gfvalvo/TeensyPOV/Hardware/20180509_212900.jpg

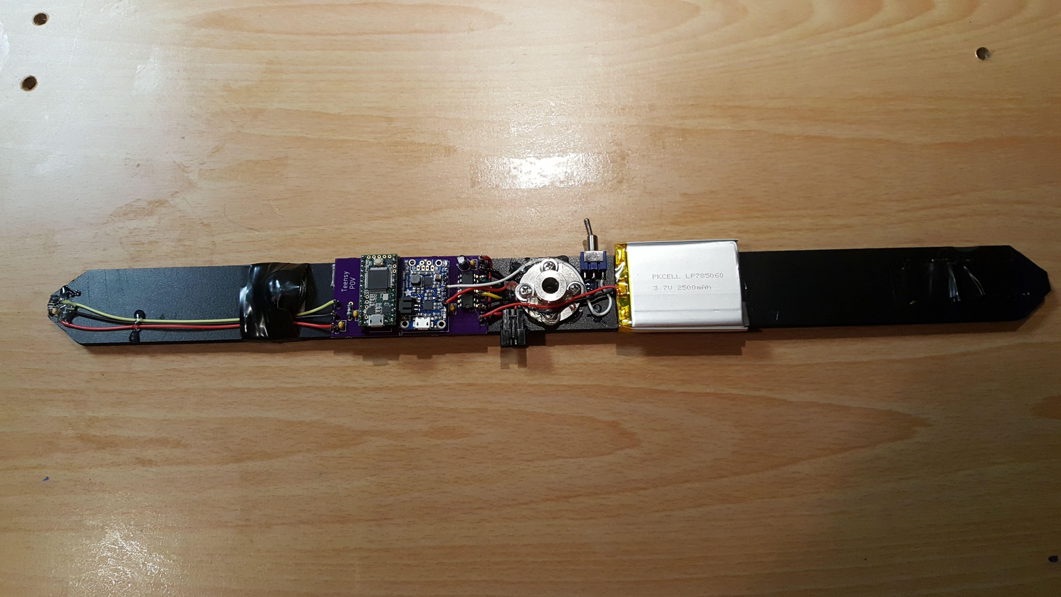
Hardware/20180509_212900.jpg
