gfvalvo/TeensyPOV/textCharacters.cpp

// MSB = topmost pixel on column
// Lowest index = leftmost column of character
// Each element in the data array is the state of one column in the letter.

#include "textCharacters.h"

const pov_char textCharacters::font_numbers[] = { { 0b0111110, 0b1000101,
		0b1001001, 0b1010001, 0b0111110, }, // 0
		{ 0b0000000, 0b0100001, 0b1111111, 0b0000001, 0b0000000, }, // 1
		{ 0b0100001, 0b1000011, 0b1000101, 0b1001001, 0b0110001, }, // 2
		{ 0b1000010, 0b1000001, 0b1010001, 0b1101001, 0b1000110, }, // 3
		{ 0b0001100, 0b0010100, 0b0100100, 0b1111111, 0b0000100, }, // 4
		{ 0b1110010, 0b1010001, 0b1010001, 0b1010001, 0b1001110, }, // 5
		{ 0b0011110, 0b0101001, 0b1001001, 0b1001001, 0b0000110, }, // 6
		{ 0b1100000, 0b1000000, 0b1000111, 0b1001000, 0b1110000, }, // 7
		{ 0b0110110, 0b1001001, 0b1001001, 0b1001001, 0b0110110, }, // 8
		{ 0b0110000, 0b1001001, 0b1001001, 0b1001010, 0b0111100, }, // 9
		};

const pov_char textCharacters::font_uppercase[] = { { 0b0111111, 0b1000100,
		0b1000100, 0b1000100, 0b0111111, }, // A
		{ 0b1111111, 0b1001001, 0b1001001, 0b1001001, 0b0110110, }, // B
		{ 0b0111110, 0b1000001, 0b1000001, 0b1000001, 0b0100010, }, // C
		{ 0b1111111, 0b1000001, 0b1000001, 0b0100010, 0b0011100, }, // D
		{ 0b1111111, 0b1001001, 0b1001001, 0b1001001, 0b1000001, }, // E
		{ 0b1111111, 0b1001000, 0b1001000, 0b1001000, 0b1000000, }, // F
		{ 0b0111110, 0b1000001, 0b1001001, 0b1001001, 0b0101111, }, // G
		{ 0b1111111, 0b0001000, 0b0001000, 0b0001000, 0b1111111, }, // H
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
				flippedColumn <<= 1;
				flippedColumn |= orignalColumn & 0b1;
				orignalColumn >>= 1;
			}
			*(matrixBuffer++) = flippedColumn;
		}
	} else {
		for (index1 = 0; index1 < 5; index1++) {
			*(matrixBuffer++) = currentCharMatrix->data[index1];
		}
	}
}
