gfvalvo/TeensyPOV/examples/MultipleDisplays/picture.cpp

/*
 * picture.cpp
 *
 *  Created on: Mar 30, 2018
 *      Author: GFV
 */
#include <stdint.h>
#include "TeensyPOV.h"
extern const LedArrayStruct pictureStruct;

static const uint8_t logNumSegments = TeensyPOV::LOG_256_SEGMENTS;
static const uint32_t numColorBits = TeensyPOV::COLOR_BITS_4;
static const uint32_t tdcDisplaySegment = 0;

static const uint32_t pictureArray[][5] = { { 0x11111111, 0x22BC2111,
		0x11111190,
		0x11111111, 0x00000011 }, { 0x11111111, 0x22BC2111, 0x11111190,
		0x11111111, 0x00000011 }, { 0x11111111, 0x22222111, 0x11111102,
		0x11111111, 0x00000011 }, { 0x11111111, 0xB2222111, 0x11111110,
		0x11111111, 0x00000611 }, { 0x11111111, 0xB222D111, 0x11111110,
		0x11111111, 0x00000511 }, { 0x11111111, 0x0002D111, 0x11111020,
		0x11111111, 0x00000511 }, { 0x11111111, 0x22000111, 0x11111122,
		0x11111111, 0x00005111 }, { 0x11111111, 0x22220111, 0x11110202,
		0x11111111, 0x00006111 }, { 0x11111111, 0x22222111, 0x11119222,
		0x11111111, 0x00005111 }, { 0x11111111, 0x22222111, 0x11162222,
		0x11111111, 0x00001111 }, { 0x11111111, 0x2222D111, 0x11002222,
		0x11111111, 0x00001111 }, { 0x11111111, 0x2222D111, 0x11922222,
		0x11111111, 0x00001111 }, { 0x11111111, 0x2022A111, 0x10222222,
		0x11111111, 0x00005111 }, { 0x11111111, 0x2002A111, 0x15222222,
		0x11111111, 0x0000A111 }, { 0x11119111, 0x02025111, 0x1D222220,
		0x11111111, 0x00001111 }, { 0x11119111, 0x88225111, 0x0222220D,
		0x11111111, 0x00001111 }, { 0x11119111, 0x08222111, 0x02222208,
		0x11111111, 0x00001111 }, { 0x11119111, 0x80822D11, 0x22222208,
		0x11111111, 0x00001111 }, { 0x11519111, 0x80005511, 0x22222268,
		0x11111116, 0x00001111 }, { 0x11519111, 0x88005551, 0x22222008,
		0x1111111C, 0x00001111 }, { 0x11519111, 0x08802951, 0x22222088,
		0x1111116B, 0x00001111 }, { 0x11519111, 0x08822951, 0x22222088,
		0x11111112, 0x00001111 }, { 0x15111111, 0x00882212, 0x22222080,
		0x11111162, 0x00001111 }, { 0x15111111, 0x00882212, 0x22222080,
		0x11111122, 0x00001111 }, { 0x1A111111, 0x0880D292, 0x22222880,
		0x11111922, 0x00001111 }, { 0x2A111111, 0x06802225, 0x22220086,
		0x11111022, 0x00001111 }, { 0x25511111, 0x06882225, 0x22222886,
		0x11111022, 0x00001111 }, { 0x05111111, 0x88802225, 0x22220880,
		0x11111C22, 0x00001111 }, { 0x05151111, 0x88802222, 0x22220088,
		0x11111022, 0x00001111 }, { 0x05151111, 0x88802222, 0x22222808,
		0x11111222, 0x00001111 }, { 0x01111111, 0x88822222, 0x22222208,
		0x11111022, 0x00001111 }, { 0x01111111, 0x88022222, 0x22222288,
		0x11111222, 0x00001111 }, { 0x11111111, 0x88022222, 0x22222080,
		0x11110022, 0x00001111 }, { 0xD1111111, 0x80222222, 0x22222020,
		0x11111222, 0x00004419 }, { 0xD1111111, 0xD2222222, 0x22222220,
		0x11116022, 0x00004441 }, { 0xD1111111, 0x2C222222, 0x22222222,
		0x11111222, 0x00001441 }, { 0x01111111, 0x22222222, 0x22222222,
		0x11111222, 0x00001111 }, { 0x01111111, 0x22222222, 0x22222222,
		0x11111022, 0x00001111 }, { 0x11111111, 0x22222222, 0x22222222,
		0x11111222, 0x00001111 }, { 0x11111111, 0x22222222, 0x22222222,
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

static const uint32_t colorTable[] = { 0x00000000, 0x00FFFF00, 0x00FFFFFF,
		0x00FF5B00, 0x00FFFF00, 0x00000000, 0x00000000, 0x00FF0000, 0x0000FFFF,
		0x00FFFF00, 0x00000000, 0x00000000, 0x00FFFFFF, 0x00FFFFFF, 0x00FFFFFF,
		0x00FF0000 };

const LedArrayStruct pictureStruct = { &pictureArray[0][0], &colorTable[0],
		numColorBits, logNumSegments, 5, tdcDisplaySegment };
