gfvalvo/TeensyPOV/examples/SimpleBitmap/colorCross.cpp

#include <stdint.h>
#include "TeensyPOV.h"

extern const LedArrayStruct colorCrossStruct;

static const uint8_t logNumSegments = TeensyPOV::LOG_128_SEGMENTS;
static const uint32_t numColorBits = TeensyPOV::COLOR_BITS_2;
static const uint32_t tdcDisplaySegment = 0;
static const uint32_t numColumns = 4;

static const uint32_t crossColors[] ={ 0x00000000, 0x00FF0000, 0x0000FF00, 0x000000FF};

static const uint32_t crossArray[][numColumns] =
{ {0x55555555, 0x55555555, 0x55555555},
  {0x00000000, 0x00000000, 0x00000000},
  {0x00000000, 0x00000000, 0x00000000},
  {0x00000000, 0x00000000, 0x00000000},
  {0x00000000, 0x00000000, 0x00000000},
  {0x00000000, 0x00000000, 0x00000000},
  {0x00000000, 0x00000000, 0x00000000},
  {0x00000000, 0x00000000, 0x00000000},
  {0x00000000, 0x00000000, 0x00000000},
  {0x00000000, 0x00000000, 0x00000000},
  {0x00000000, 0x00000000, 0x00000000},
  {0x00000000, 0x00000000, 0x00000000},
  {0x00000000, 0x00000000, 0x00000000},
  {0x00000000, 0x00000000, 0x00000000},
  {0x00000000, 0x00000000, 0x00000000},
  {0x00000000, 0x00000000, 0x00000000},
  {0x00000000, 0x00000000, 0x00000000},
  {0x00000000, 0x00000000, 0x00000000},
  {0x00000000, 0x00000000, 0x00000000},
  {0x00000000, 0x00000000, 0x00000000},
  {0x00000000, 0x00000000, 0x00000000},
  {0x00000000, 0x00000000, 0x00000000},
  {0x00000000, 0x00000000, 0x00000000},
  {0x00000000, 0x00000000, 0x00000000},
  {0x00000000, 0x00000000, 0x00000000},
  {0x00000000, 0x00000000, 0x00000000},
  {0x00000000, 0x00000000, 0x00000000},
  {0x00000000, 0x00000000, 0x00000000},
  {0x00000000, 0x00000000, 0x00000000},
  {0x00000000, 0x00000000, 0x00000000},
  {0x00000000, 0x00000000, 0x00000000},
  {0x00000000, 0x00000000, 0x00000000},
  {0xAAAAAAAA, 0xAAAAAAAA, 0xAAAAAAAA},
  {0x00000000, 0x00000000, 0x00000000},
  {0x00000000, 0x00000000, 0x00000000},
  {0x00000000, 0x00000000, 0x00000000},
  {0x00000000, 0x00000000, 0x00000000},
  {0x00000000, 0x00000000, 0x00000000},
  {0x00000000, 0x00000000, 0x00000000},
  {0x00000000, 0x00000000, 0x00000000},
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
};

const LedArrayStruct colorCrossStruct = { &crossArray[0][0], &crossColors[0],
		numColorBits, logNumSegments, numColumns, tdcDisplaySegment };
